radhoo/uradmonitor_kit1/pcb/1.2.105/circuit/kit1_105_top.png

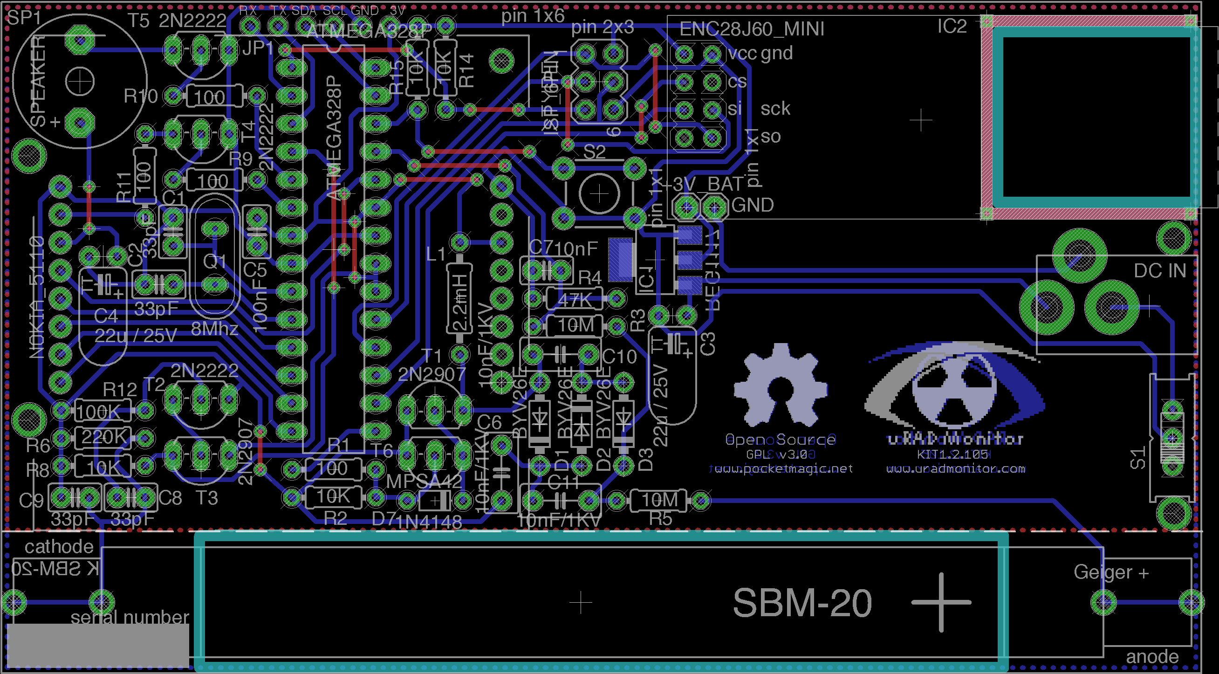
pcb/1.2.105/circuit/kit1_105_top.png
