radhoo/uradmonitor_kit1/pcb/kit1_improvements_c.jpg

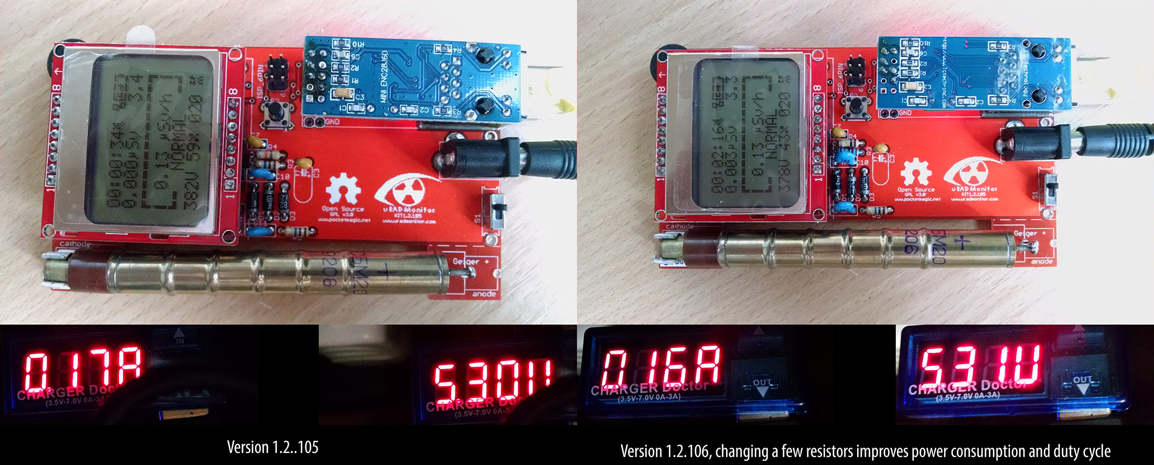
pcb/kit1_improvements_c.jpg
