radhoo/uradmonitor_kit1/pcb/pcb-1.1.103/circuit/pcb_103_2.png

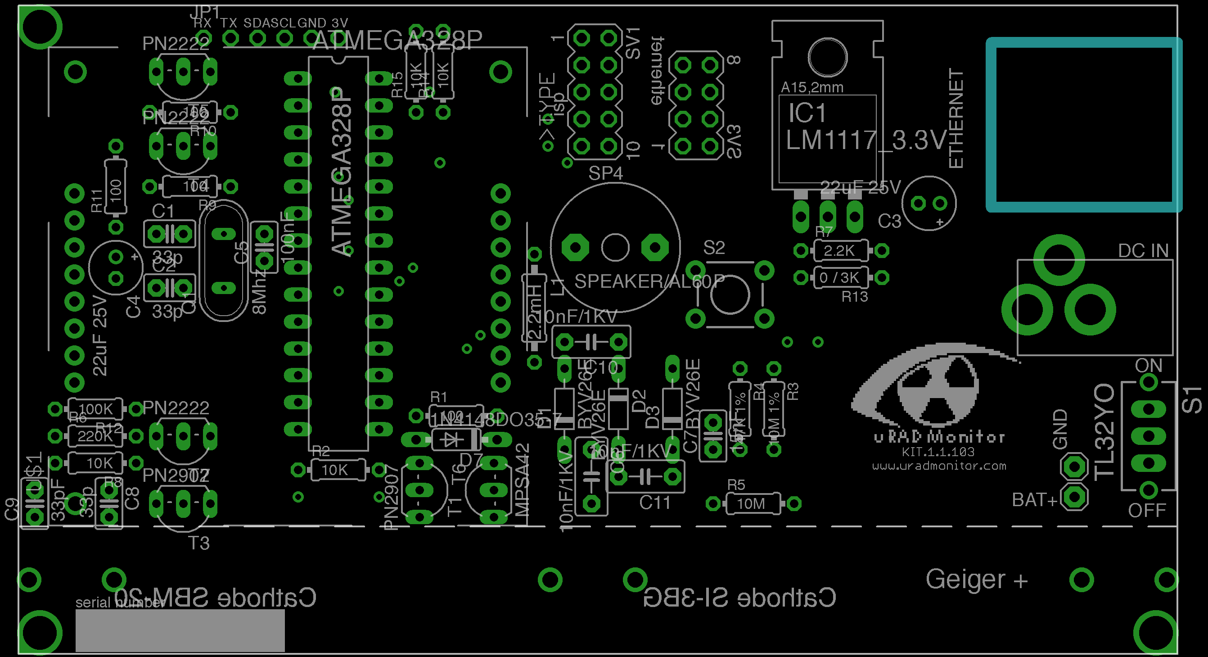
pcb/pcb-1.1.103/circuit/pcb_103_2.png
