radhoo/uradmonitor_kit1/pcb/pcb-1.1.103/circuit/sch_103_1.png

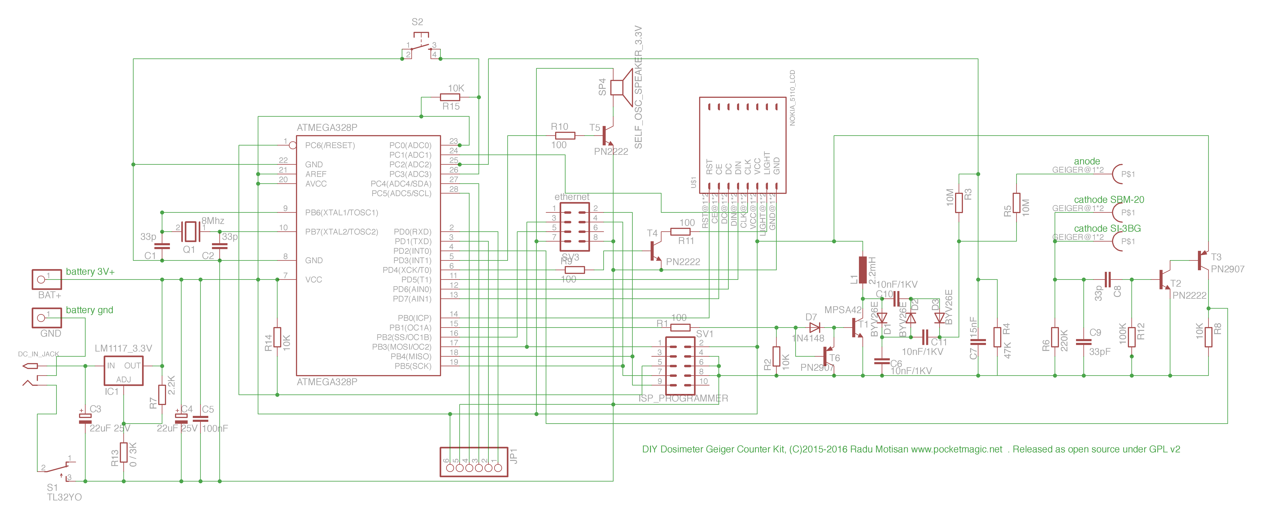
pcb/pcb-1.1.103/circuit/sch_103_1.png
