radhoo/uradmonitor_kit1/pcb/pcb-1.1.103/pictures/4.jpg

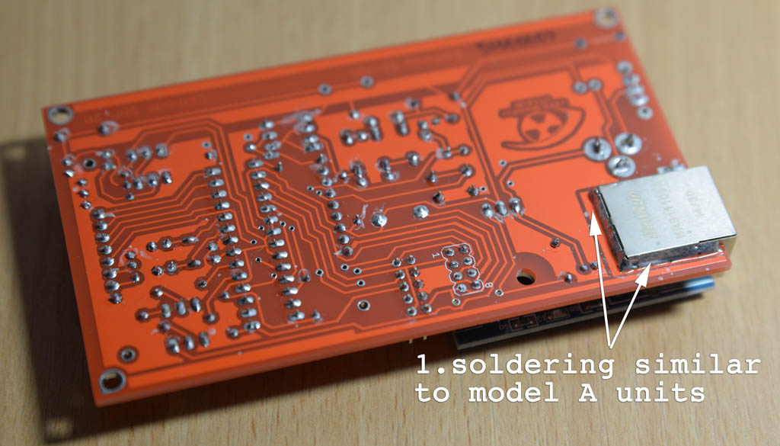
pcb/pcb-1.1.103/pictures/4.jpg
