radhoo/uradmonitor_kit1/pcb/pcb-1.1.103/pictures/5.jpg

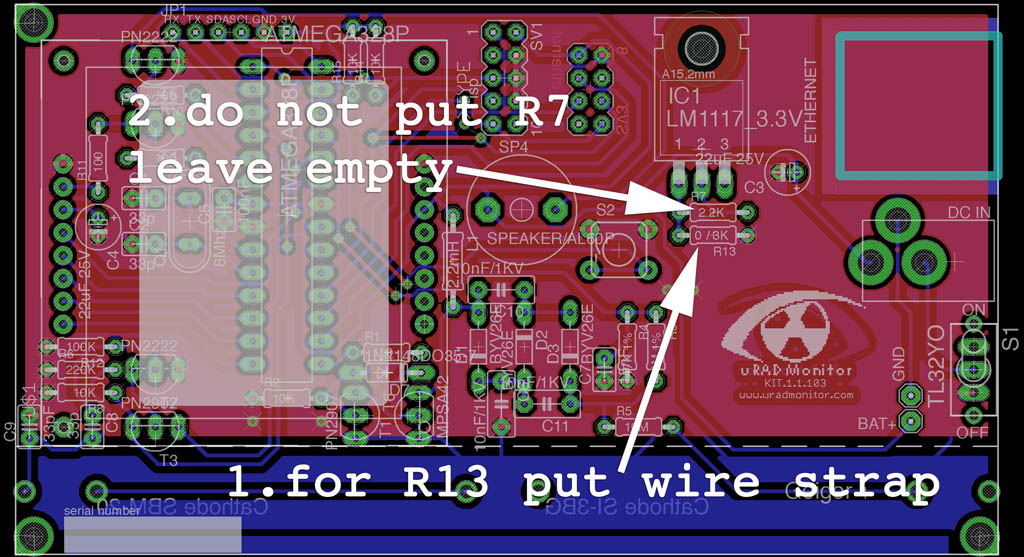
pcb/pcb-1.1.103/pictures/5.jpg
