radhoo/uradmonitor_kit1/pcb/pcb-1.1.103/pictures/firmware.jpg

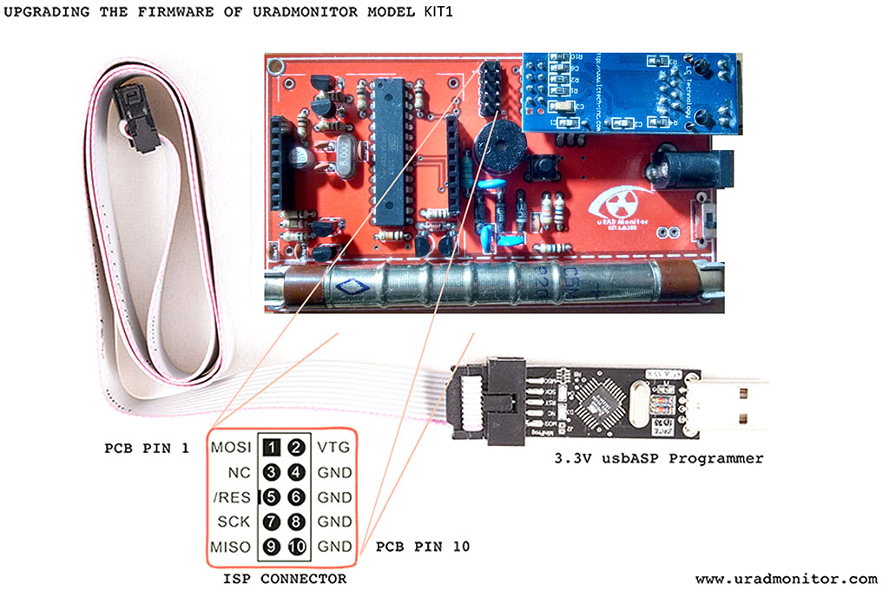
pcb/pcb-1.1.103/pictures/firmware.jpg
