radhoo/uradmonitor_kit1/pcb/pcb-1.1/res/uRADMonitor_KIT1.1_pcbmask.png

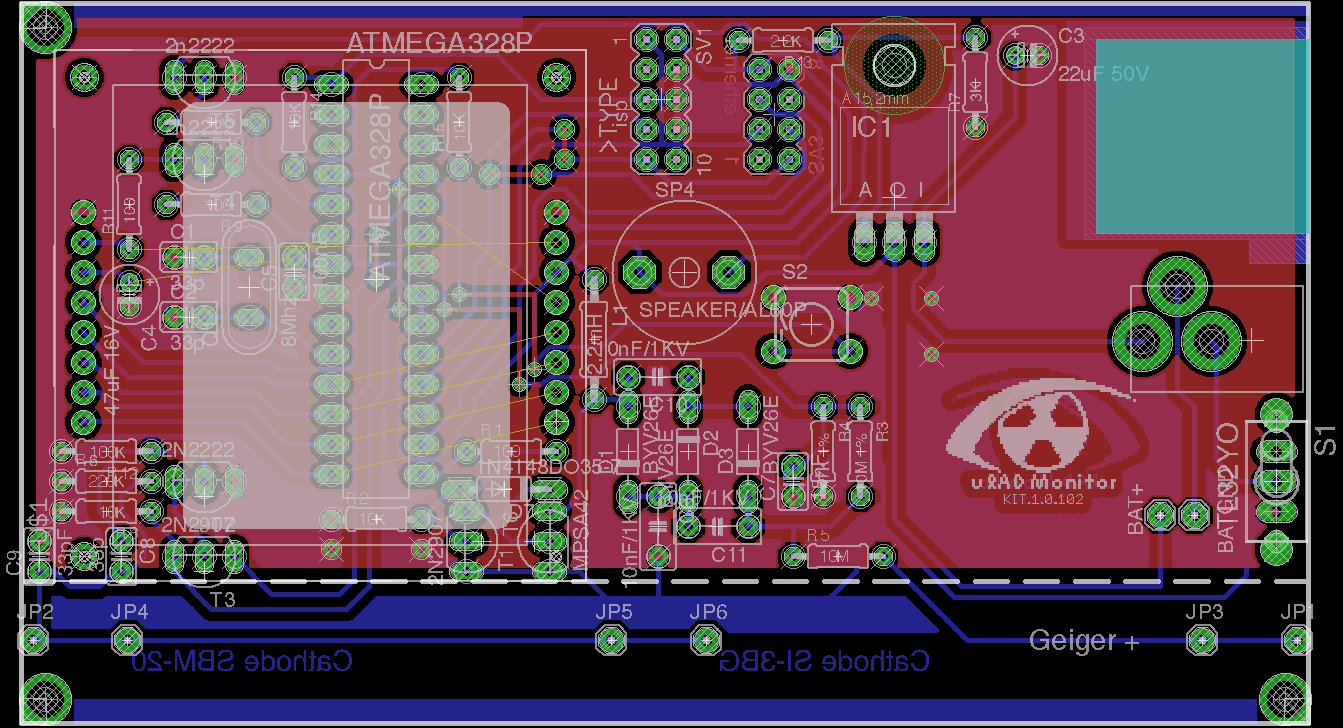
pcb/pcb-1.1/res/uRADMonitor_KIT1.1_pcbmask.png
