radhoo/uradmonitor_kit1/code/124/misc/expProtocol.h

/**
 *	File:       	expProtocol.h
 *	Version:  		1.0
 *	Date:       	2016
 *	License:		GPL v3
 *	Description:	exp is a restful api compatible protocol for uRADMonitor KIT1 data upload
 *	Project:		uRADMonitor KIT1, a hackable digital sensor monitoring tool with network interface
 *
 *	Copyright 2016 by Radu Motisan, radu.motisan@gmail.com
 *	Copyright 2016 by Magnasci SRL, www.magnasci.com
 *
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
 *	You should have received a copy of the GNU General Public License
 *	along with this program.  If not, see <http://www.gnu.org/licenses/>.
 */

#define ID_TIME_SECONDS "01"			// compulsory: local time in seconds
#define ID_TEMPERATURE_CELSIUS "02"		// optional: temperature in degrees celsius
#define ID_PRESSURE_PASCALS "03"		// optional: barometric pressure in pascals
#define ID_HUMIDITY_RH "04"				// optional: humidity as relative humidity in percentage %
#define ID_LUMINOSITY_RL "05"			// optional: luminosity as relative luminosity in percentage ‰
#define ID_VOC_OHM "06"					// optional: volatile organic compounds in ohms
#define ID_CO2_PPM "07"					// optional: carbon dioxide in ppm
#define ID_CH2O_PPM "08"				// optional: formaldehyde in ppm
#define ID_PM25_UGCM "09"				// optional: particulate matter in micro grams per cubic meter
#define ID_BATTERY_VOLTS "0A"			// optional: device battery voltage in volts
#define ID_GEIGER_CPM "0B"				// optional: radiation measured on geiger tube in cpm
#define ID_INVERTERVOLTAGE_VOLTS "0C"	// optional: high voltage geiger tube inverter voltage in volts
#define ID_INVERTERDUTY_PM "0D"			// optional: high voltage geiger tube inverter duty in ‰
#define ID_VERSION_HW "0E"				// optional: hardware version
#define ID_VERSION_SW "0F"				// optional: software firmware version
#define ID_TUBE "10"					// optional: tube type ID
#define ID_NOISE "11"					// optional: noise in dB
#define ID_PM1_UGCM "12"				// optional: particulate matter in micro grams per cubic meter
#define ID_PM10_UGCM "13"				// optional: particulate matter in micro grams per cubic meter
#define ID_O3_PPB "14"					// optional: ozone in ppb
