radhoo/uradmonitor_kit1/code/misc/models.h

#pragma once

// define device models
#define MODEL_A 0x1
#define MODEL_B 0x2
#define MODEL_C 0x3
#define MODEL_A2 0x4
#define MODEL_KIT1 0x5
#define MODEL_D 0x6
//1=model_A, 2=model_B, 3=model_C, 4=model_A2, 9=model_0
